demianzenkov/UWB-Open-RTLS-MCU/hardware/anchor/Photos/anchor_asm.png

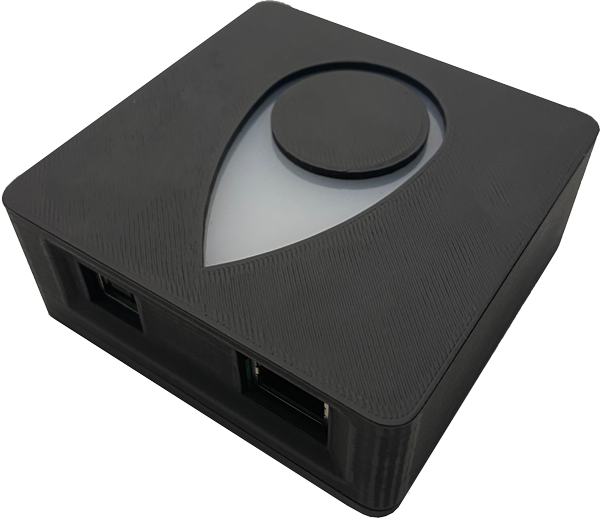
hardware/anchor/Photos/anchor_asm.png
