demianzenkov/UWB-Open-RTLS-MCU/hardware/anchor/Photos/anchor_case.png

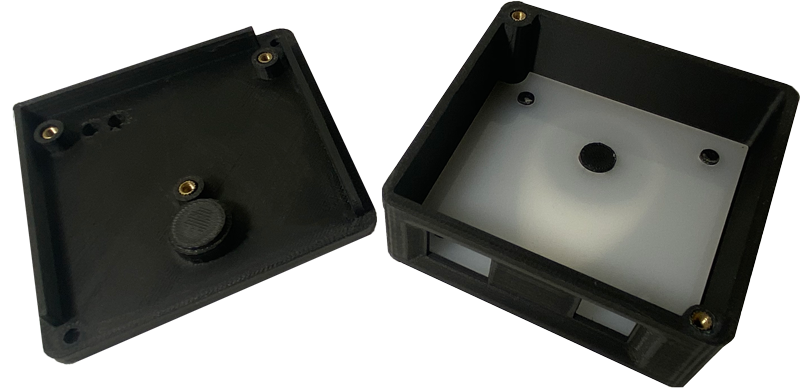
hardware/anchor/Photos/anchor_case.png
