demianzenkov/UWB-Open-RTLS-MCU/hardware/anchor/Photos/anchor_pcb.png

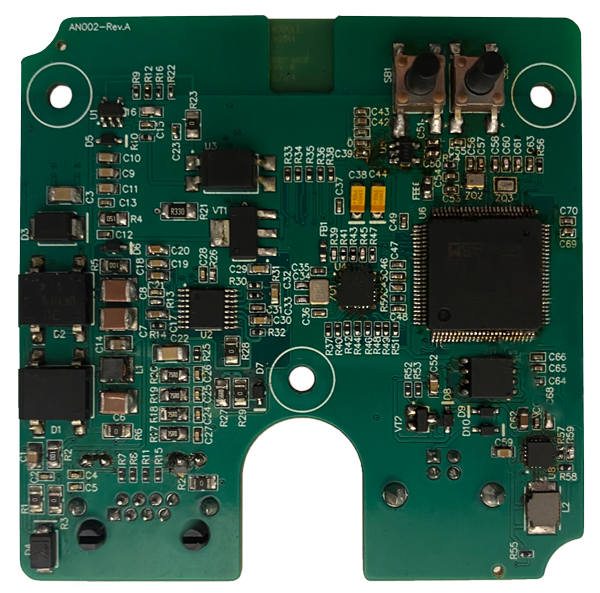
hardware/anchor/Photos/anchor_pcb.png
