demianzenkov/UWB-Open-RTLS-MCU/hardware/anchor/Photos/IMG_0143.JPG

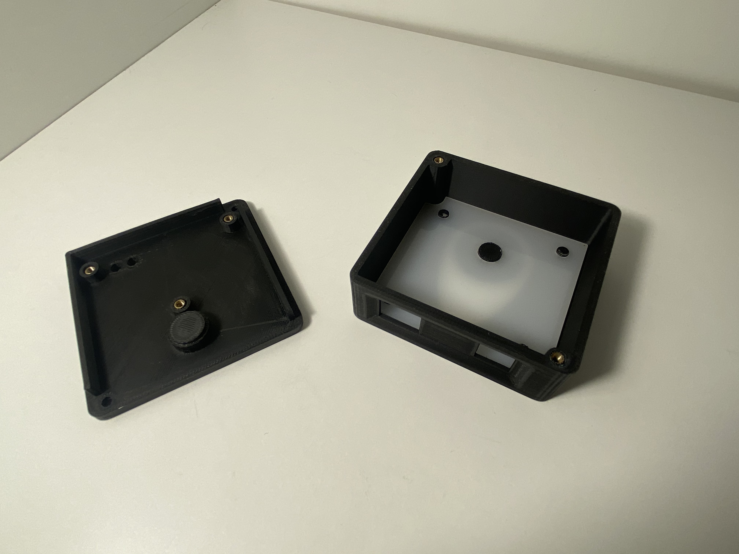
hardware/anchor/Photos/IMG_0143.JPG
