demianzenkov/UWB-Open-RTLS-MCU/hardware/anchor/Photos/IMG_0152.JPG

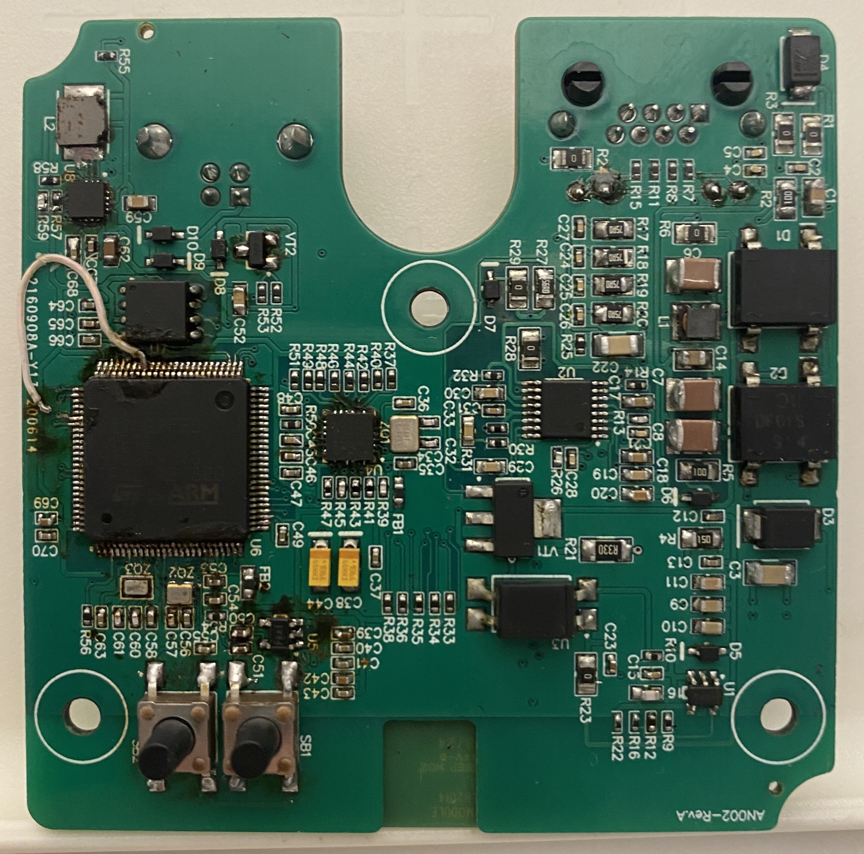
hardware/anchor/Photos/IMG_0152.JPG
