demianzenkov/UWB-Open-RTLS-MCU/hardware/anchor/Photos/IMG_0156.JPG

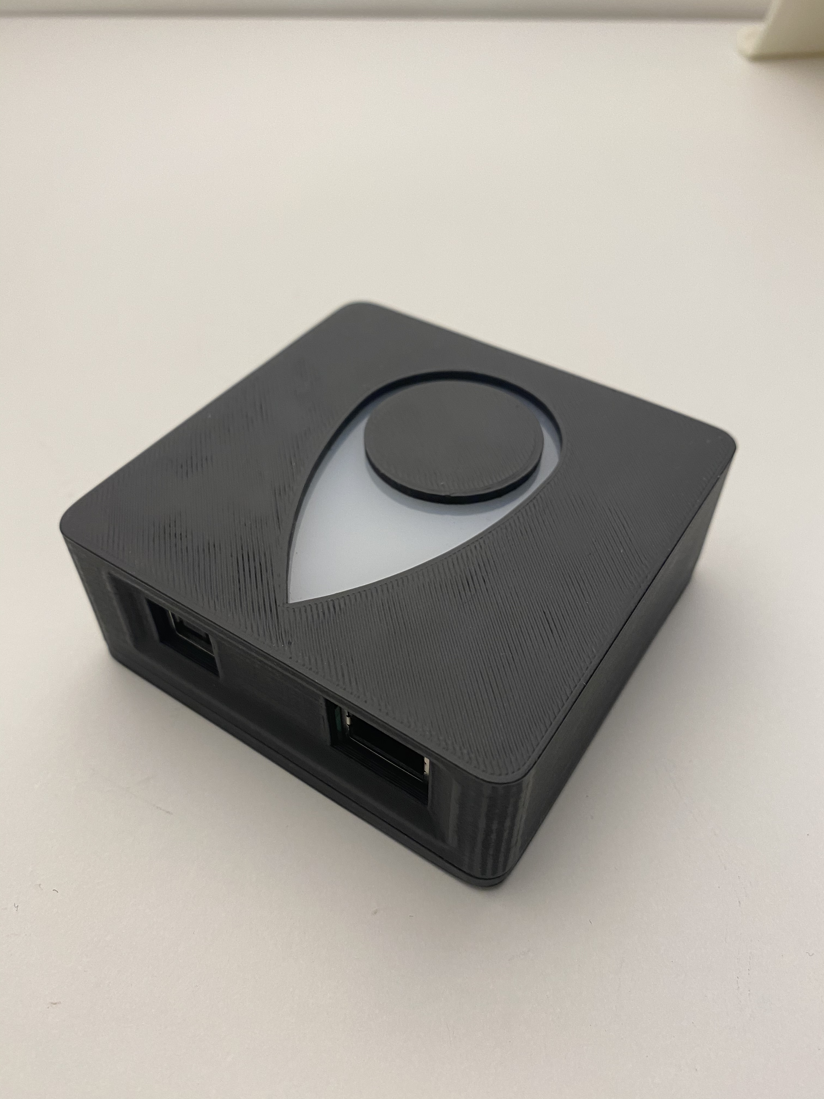
hardware/anchor/Photos/IMG_0156.JPG
