demianzenkov/UWB-Open-RTLS-MCU/hardware/anchor/Photos/IMG_0158.JPG

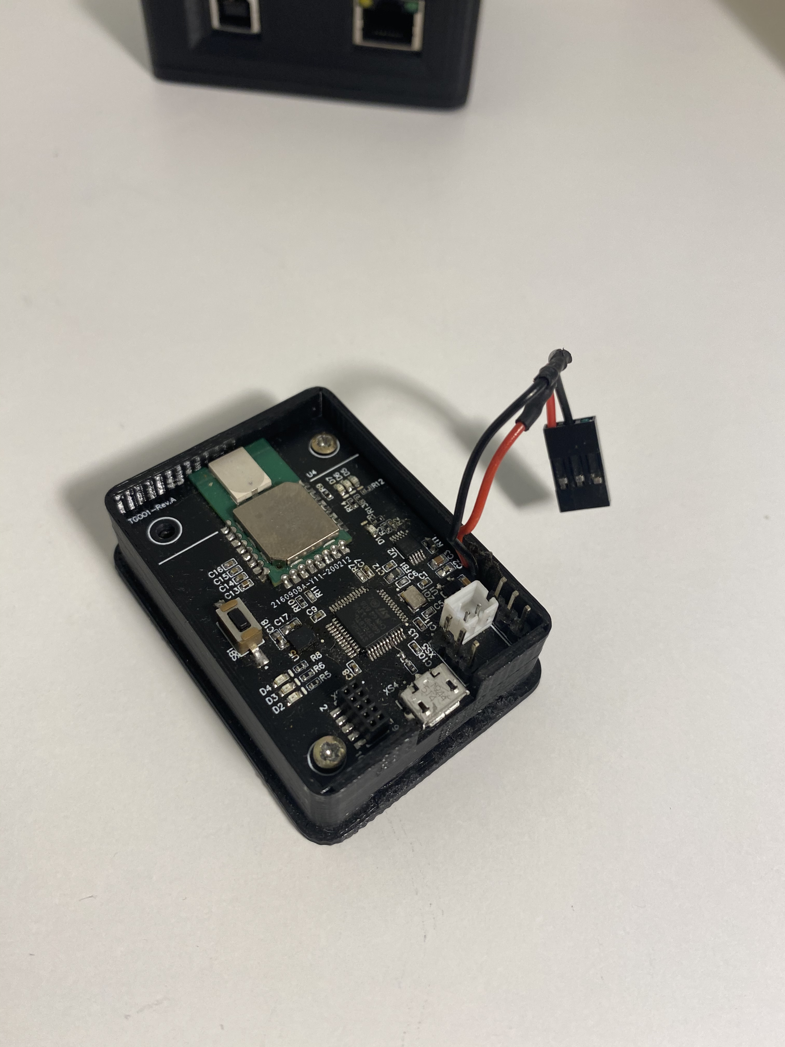
hardware/anchor/Photos/IMG_0158.JPG
