demianzenkov/UWB-Open-RTLS-MCU/hardware/anchor/Photos/IMG_0159.JPG

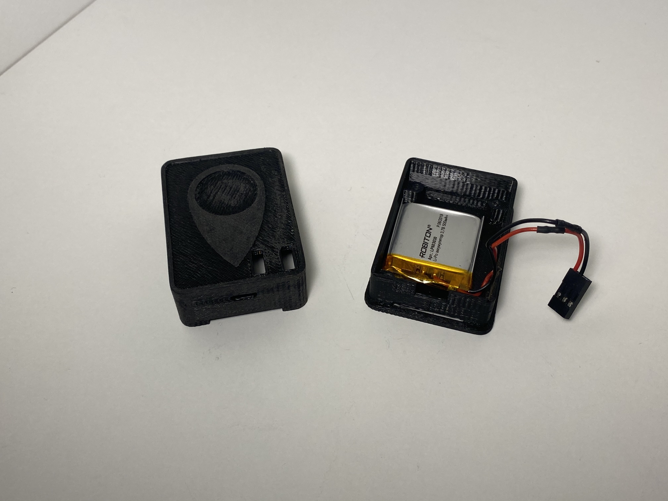
hardware/anchor/Photos/IMG_0159.JPG
