demianzenkov/UWB-Open-RTLS-MCU/hardware/anchor/Photos/IMG_0161.JPG

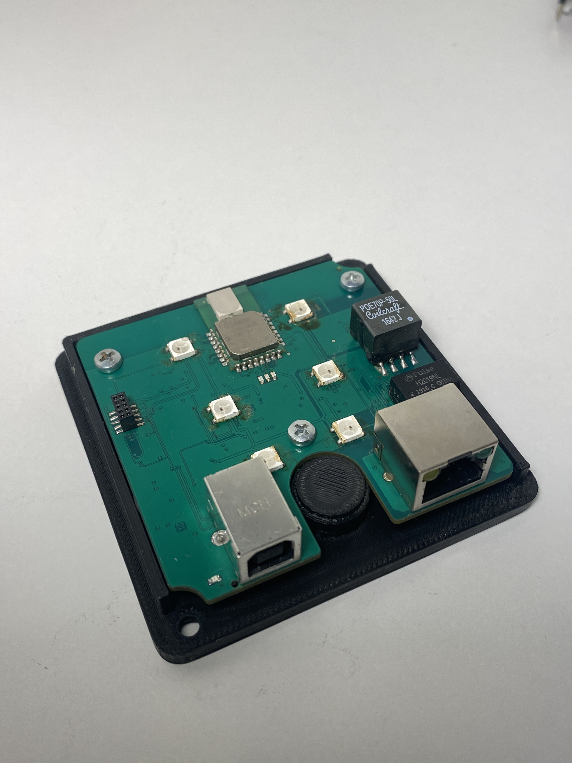
hardware/anchor/Photos/IMG_0161.JPG
