demianzenkov/UWB-Open-RTLS-MCU/hardware/anchor/Photos/tag_case.png

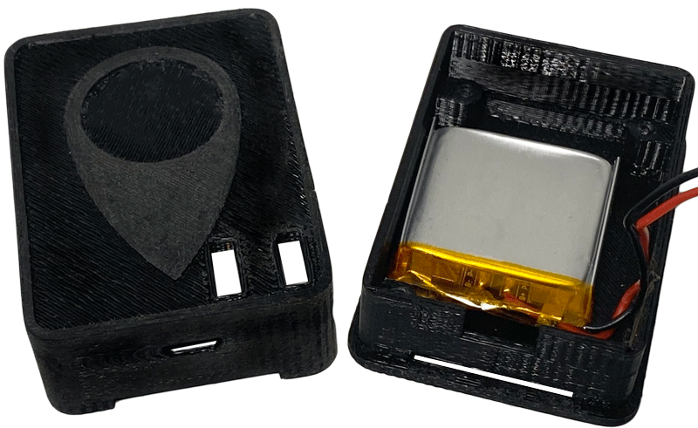
hardware/anchor/Photos/tag_case.png
