demianzenkov/UWB-Open-RTLS-MCU/hardware/anchor/Render/an_tag.png

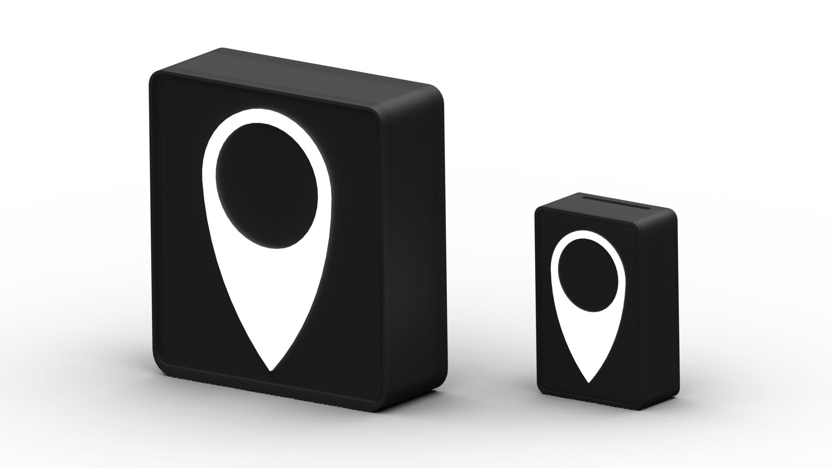
hardware/anchor/Render/an_tag.png
