demianzenkov/UWB-Open-RTLS-MCU/hardware/anchor/Render/AN_TAG_04.png

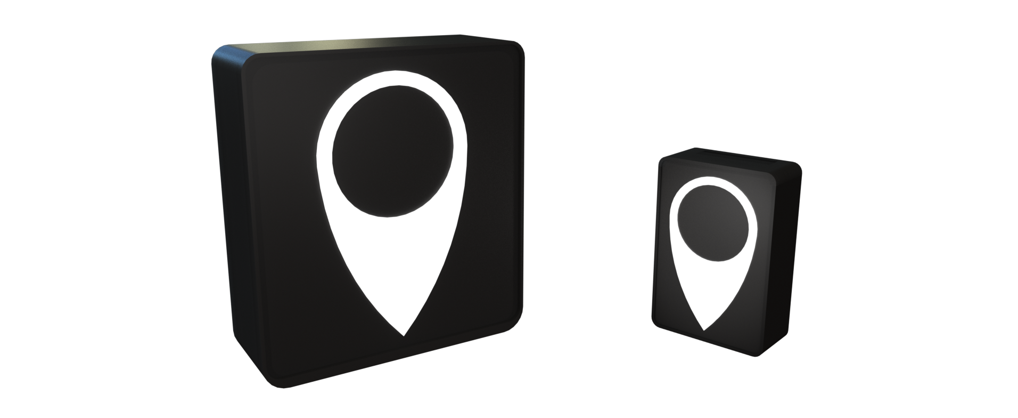
hardware/anchor/Render/AN_TAG_04.png
