demianzenkov/UWB-Open-RTLS-MCU/docs/anchor_assembly.gif

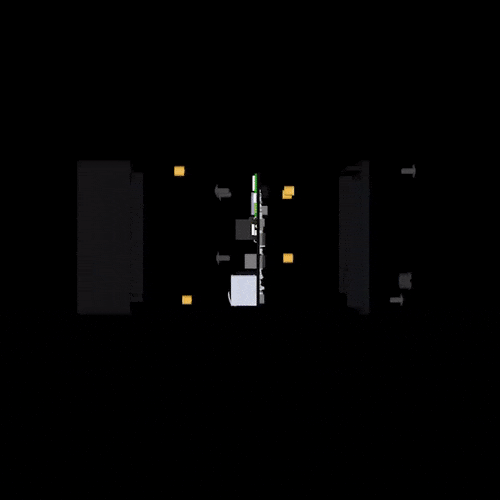
docs/anchor_assembly.gif
