demianzenkov/UWB-Open-RTLS-MCU/firmware/tag/User/Modules/une_twr.h

#define __UNE_TWR
#include "prj_defs.h"
#include "dwm1000.h"
#define UUS_TO_DWT_TIME 65536
#define POLL_TX_TO_RESP_RX_DLY_UUS 500
#define RESP_RX_TO_FINAL_TX_DLY_UUS 3100 //3000
#define RESP_RX_TIMEOUT_UUS 2700 	//2700 // Receive response timeout. NOTE 5
#define POLL_RX_TO_RESP_TX_DLY_UUS 3500				//2750
#define RESP_TX_TO_FINAL_RX_DLY_UUS 1000		//500
#define FINAL_RX_TIMEOUT_UUS 3700
#define PRE_TIMEOUT 8 			// Preamble tomeout. NOTE 6
#define POLL_MSG_SIZE	10
#define RESP_MSG_SIZE	12
#define FINAL_MSG_SIZE	29
#define DW_MSG_PREAMBLE_LEN	4
#define DEFAULT_TAG_ID		0x01
#define DEFAULT_ANCHOR_ID	0x01
#define START_POLL_N_H	0
#define START_POLL_N_L	0
#define START_RESP_N_H	0
#define START_RESP_N_L	0
#define START_FINAL_N_H	0
#define START_FINAL_N_L	0
#define MSG_TS_LEN 		5
#define FINAL_MSG_POLL_TX_TS_IDX	12
#define FINAL_MSG_RESP_RX_TS_IDX	17
#define FINAL_MSG_FINAL_TX_TS_IDX	22
#define MSG_TAG_IDX		4
#define MSG_AN_IDX		5
#define MSG_POLL_H_IDX		6
#define MSG_POLL_L_IDX		7
#define MSG_RESP_H_IDX		8
#define MSG_RESP_L_IDX		9
#define MSG_FINAL_H_IDX		10
#define MSG_FINAL_L_IDX		11
#define SPEED_OF_LIGHT 299702547	// metres per second
class UNE_TWR {
public:
  UNE_TWR(DWM1000 * dwm);
  ~UNE_TWR();
  static void initDWM();
  S08 twrInitiatorLoop(U08 an_id);
  S08 twrResponderLoop();
  static void final_msg_set_ts(uint8 *ts_field, uint64 ts);
  static void final_msg_get_ts(const uint8 *ts_field, uint64 *ts);
private:
  DWM1000 * dwm;
  U16 poll_frame_seq_nb;	// Tag
  U16 resp_frame_seq_nb;	// Anchor
  U16 final_frame_seq_nb;	// Tag
  U64 poll_rx_ts; 	// anchor(responder)
  U64 resp_tx_ts;	// anchor(responder)
  U64 final_rx_ts;	// anchor(responder)
  U64 poll_tx_ts;	// tag(initiator)
  U64 resp_rx_ts;	// tag(initiator)
  U64 final_tx_time;	// tag(initiator)
  U64 final_tx_ts;	// tag(initiator)
  U08 tag_id;		// anchor(initiator)
  double tof;		// anchor(initiator)
  float distance;	// anchor(initiator)
  U08 poll_msg[POLL_MSG_SIZE] = {'T', 'W', 'R', 'P',
			DEFAULT_TAG_ID,
			DEFAULT_ANCHOR_ID,
			START_POLL_N_H,
			START_POLL_N_L,
  			0, 0};		// CRC
  U08 resp_msg[RESP_MSG_SIZE] = {'T', 'W', 'R', 'R',
  			DEFAULT_TAG_ID,
			DEFAULT_ANCHOR_ID,
			START_POLL_N_H,
			START_POLL_N_L,
			START_RESP_N_H,
			START_RESP_N_L,
  			0, 0};		// CRC
  U08 final_msg[FINAL_MSG_SIZE] = {'T', 'W', 'R', 'F',
			DEFAULT_TAG_ID,
			DEFAULT_ANCHOR_ID,
			START_POLL_N_H,
			START_POLL_N_L,
			START_RESP_N_H,
			START_RESP_N_L,
			START_FINAL_N_H,
			START_FINAL_N_L,
			0,0,0,0,0,	// POLL TX
			0,0,0,0,0,	// RESP RX
			0,0,0,0,0,	// FINAL TX
  			0, 0};		// CRC
};
