demianzenkov/UWB-Open-RTLS-MCU/firmware/anchor/Inc/main.h

#define DW_WUP_Pin GPIO_PIN_2
#define DW_WUP_GPIO_Port GPIOE
#define DW_RESET_Pin GPIO_PIN_3
#define DW_RESET_GPIO_Port GPIOE
#define DW_RESET_EXTI_IRQn EXTI3_IRQn
#define DW_IRQn_Pin GPIO_PIN_4
#define DW_IRQn_GPIO_Port GPIOE
#define DW_IRQn_EXTI_IRQn EXTI4_IRQn
#define DW_NSS_Pin GPIO_PIN_4
#define DW_NSS_GPIO_Port GPIOA
#define DW_SCK_Pin GPIO_PIN_5
#define DW_SCK_GPIO_Port GPIOA
#define DW_MISO_Pin GPIO_PIN_6
#define DW_MISO_GPIO_Port GPIOA
#define FLASH_SCK_Pin GPIO_PIN_10
#define FLASH_SCK_GPIO_Port GPIOB
#define FLASH_MISO_Pin GPIO_PIN_14
#define FLASH_MISO_GPIO_Port GPIOB
#define FLASH_MOSI_Pin GPIO_PIN_15
#define FLASH_MOSI_GPIO_Port GPIOB
#define FLASH_CS_Pin GPIO_PIN_8
#define FLASH_CS_GPIO_Port GPIOD
#define LED_DIN_Pin GPIO_PIN_8
#define LED_DIN_GPIO_Port GPIOA
#define LED_VDD_Pin GPIO_PIN_1
#define LED_VDD_GPIO_Port GPIOD
#define DW_MOSI_Pin GPIO_PIN_5
#define DW_MOSI_GPIO_Port GPIOB
