demianzenkov/UWB-Open-RTLS-MCU/firmware/tag/Src/main.cpp

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

/* Includes ------------------------------------------------------------------*/
#include "main.h"
#include "cmsis_os.h"
#include "usb_device.h"

/* USER CODE BEGIN Includes */
#include "tsk_dwm.h"
#include "tsk_lsm.h"
#include "tsk_usb.h"
#include "tsk_event.h"
#include "settings.h"

/* USER CODE END Includes */

SPI_HandleTypeDef hspi1;
SPI_HandleTypeDef hspi2;

TIM_HandleTypeDef htim6;

UART_HandleTypeDef huart1;

osThreadId initTaskHandle;
/* USER CODE BEGIN PV */
extern TskDWM tskDWM;
extern TskLSM tskLSM;
extern TskUSB tskUSB;
extern TskEvent tskEvent;

extern DeviceSettings settings;
volatile uint32_t us_tick = 0;
/* USER CODE END PV */


static void MX_GPIO_Init(void);
static void MX_SPI1_Init(void);
static void MX_SPI2_Init(void);
static void MX_TIM6_Init(void);
static void MX_USART1_UART_Init(void);
void StartDefaultTask(void const * argument);

/**
  * @brief  The application entry point.
  * @retval int
  */
int main(void)
{
  

  /* MCU Configuration-------------------------------------------------------- */

  /* Reset of all peripherals, Initializes the Flash interface and the Systick. */
  HAL_Init();

  /* Configure the system clock */
  SystemClock_Config();

  /* Initialize all configured peripherals */
  MX_GPIO_Init();
  MX_SPI1_Init();
  MX_SPI2_Init();
  MX_USART1_UART_Init();
//  MX_TIM6_Init();
  /* USER CODE BEGIN 2 */
  settings.init();
  /* USER CODE END 2 */

  /* USER CODE BEGIN RTOS_MUTEX */
  /* add mutexes, ... */
  /* USER CODE END RTOS_MUTEX */

  /* USER CODE BEGIN RTOS_SEMAPHORES */
  /* add semaphores, ... */
  /* USER CODE END RTOS_SEMAPHORES */

  /* USER CODE BEGIN RTOS_TIMERS */
  /* start timers, add new ones, ... */
  /* USER CODE END RTOS_TIMERS */

  /* USER CODE BEGIN RTOS_QUEUES */
  /* add queues, ... */
  /* USER CODE END RTOS_QUEUES */

  /* Create the thread(s) */
  /* definition and creation of initTask */
  osThreadDef(initTask, StartDefaultTask, osPriorityNormal, 0, 128);
  initTaskHandle = osThreadCreate(osThread(initTask), NULL);

  /* USER CODE BEGIN RTOS_THREADS */
  /* add threads, ... */
  tskDWM.createTask();
  tskUSB.createTask();
  tskEvent.createTask();
//  tskLSM.createTask();
  /* USER CODE END RTOS_THREADS */

  /* Start scheduler */
  osKernelStart();
  
  /* We should never get here as control is now taken by the scheduler */

  /* Infinite loop */
  /* USER CODE BEGIN WHILE */
  while (1)
  { 
    /* USER CODE END WHILE */

    /* USER CODE BEGIN 3 */
  }
  /* USER CODE END 3 */
}

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
/* USER CODE BEGIN Header_StartDefaultTask */
/**
  * @brief  Function implementing the initTask thread.
  * @param  argument: Not used 
  * @retval None
  */
/* USER CODE END Header_StartDefaultTask */
void StartDefaultTask(void const * argument)
{                
  /* init code for USB_DEVICE */
  MX_USB_DEVICE_Init();

  /* USER CODE BEGIN 5 */
  /* Infinite loop */
  for(;;)
  {
    HAL_GPIO_TogglePin(LED1_GPIO_Port, LED1_Pin);
    osDelay(1000);
    HAL_GPIO_TogglePin(LED1_GPIO_Port, LED1_Pin);
    osDelay(1000);
  }
  /* USER CODE END 5 */ 
}

/**
  * @brief  Period elapsed callback in non blocking mode
  * @note   This function is called  when TIM3 interrupt took place, inside
  * HAL_TIM_IRQHandler(). It makes a direct call to HAL_IncTick() to increment
  * a global variable "uwTick" used as application time base.
  * @param  htim : TIM handle
  * @retval None
  */
void HAL_TIM_PeriodElapsedCallback(TIM_HandleTypeDef *htim)
{
  if (htim->Instance == TIM3) {
    HAL_IncTick();
  }
  /* USER CODE BEGIN Callback 1 */
  if (htim->Instance == TIM6){
    us_tick++;  
  }
  /* USER CODE END Callback 1 */
}

/**
  * @brief  This function is executed in case of error occurrence.
  * @retval None
  */
void Error_Handler(void)
{
  /* USER CODE BEGIN Error_Handler_Debug */
  /* User can add his own implementation to report the HAL error return state */

  /* USER CODE END Error_Handler_Debug */
}

#ifdef  USE_FULL_ASSERT
/**
  * @brief  Reports the name of the source file and the source line number
  *         where the assert_param error has occurred.
  * @param  file: pointer to the source file name
  * @param  line: assert_param error line source number
  * @retval None
  */
void assert_failed(uint8_t *file, uint32_t line)
{ 
  /* USER CODE BEGIN 6 */
  /* User can add his own implementation to report the file name and line number,
     tex: printf("Wrong parameters value: file %s on line %d\r\n", file, line) */
  /* USER CODE END 6 */
}
#endif /* USE_FULL_ASSERT */

/************************ (C) COPYRIGHT STMicroelectronics *****END OF FILE****/
