demianzenkov/UWB-Open-RTLS-MCU/firmware/anchor/User/modules/settings.h

#ifndef __DEV_SETTINGS
#define __DEV_SETTINGS

#include "settings_pb.h"
#include "net_conf.h"

#define DEFAULT_DEVICE_ID_U32		0xAABBDDCC
#define DEFAULT_TX_ANT_DLY 		16436
#define DEFAULT_RX_ANT_DLY 		16436
#define DEFAULT_TWR_ANCHOR_CNT		4
#define DEFAULT_POLL_PERIOD		1000

class DeviceSettings
{
public:
  DeviceSettings();
  S08 init();
  
  S08 setDefaultSettings();
  S08 getSettings(U08 ** buf, U16 * len);
  S08 setSettingsPb(U08 * buf, U16 len);
  
private:
  S08 readSettingsFromFlash();
  S08 writeSettingsToFlash(U08 * buf, U16 len);
  
public:
  SettingsPB pb_settings;
  NetConfig net_conf;
  
  static U08 MAC_ADDR[6];
  
};

extern DeviceSettings settings;

#endif /* __DEV_SETTINGS */
