demianzenkov/UWB-Open-RTLS-MCU/firmware/anchor/Src/lwip.cpp

/**
 ******************************************************************************
  * File Name          : LWIP.c
  * Description        : This file provides initialization code for LWIP
  *                      middleWare.
  ******************************************************************************
  * @attention
  *
  * <h2><center>&copy; Copyright (c) 2020 STMicroelectronics.
  * All rights reserved.</center></h2>
  *
  * This software component is licensed by ST under Ultimate Liberty license
  * SLA0044, the "License"; You may not use this file except in compliance with
  * the License. You may obtain a copy of the License at:
  *                             www.st.com/SLA0044
  *
  ******************************************************************************
  */
  
/* Includes ------------------------------------------------------------------*/
#include "lwip.h"
#include "lwip/init.h"
#include "lwip/netif.h"
#if defined ( __CC_ARM )  /* MDK ARM Compiler */
#include "lwip/sio.h"
#endif /* MDK ARM Compiler */

/* USER CODE BEGIN 0 */
#include "ethernetif.h"
#include "settings.h"

/* USER CODE END 0 */
/* ETH Variables initialization ----------------------------------------------*/
void Error_Handler(void);

/* Variables Initialization */
struct netif gnetif;
ip4_addr_t ipaddr;
ip4_addr_t netmask;
ip4_addr_t gw;
uint8_t IP_ADDRESS[4];
uint8_t NETMASK_ADDRESS[4];
uint8_t GATEWAY_ADDRESS[4];

/**
  * LwIP initialization function
  */
void MX_LWIP_Init(void)
{
  /* USER CODE BEGIN LWIP_INIT */
  /* IP addresses initialization */
  
  IP_ADDRESS[0] = settings.net_conf.getDeviceIp()[0];
  IP_ADDRESS[1] = settings.net_conf.getDeviceIp()[1];
  IP_ADDRESS[2] = settings.net_conf.getDeviceIp()[2];
  IP_ADDRESS[3] = settings.net_conf.getDeviceIp()[3];
  NETMASK_ADDRESS[0] = settings.net_conf.getSubnetMask()[0];
  NETMASK_ADDRESS[1] = settings.net_conf.getSubnetMask()[1];
  NETMASK_ADDRESS[2] = settings.net_conf.getSubnetMask()[2];
  NETMASK_ADDRESS[3] = settings.net_conf.getSubnetMask()[3];
  GATEWAY_ADDRESS[0] = settings.net_conf.getGatewayIp()[0];
  GATEWAY_ADDRESS[1] = settings.net_conf.getGatewayIp()[1];
  GATEWAY_ADDRESS[2] = settings.net_conf.getGatewayIp()[2];
  GATEWAY_ADDRESS[3] = settings.net_conf.getGatewayIp()[3];
  /* USER CODE END LWIP_INIT */
  
  /* Initilialize the LwIP stack with RTOS */
  tcpip_init( NULL, NULL );

  /* IP addresses initialization without DHCP (IPv4) */
  IP4_ADDR(&ipaddr, IP_ADDRESS[0], IP_ADDRESS[1], IP_ADDRESS[2], IP_ADDRESS[3]);
  IP4_ADDR(&netmask, NETMASK_ADDRESS[0], NETMASK_ADDRESS[1] , NETMASK_ADDRESS[2], NETMASK_ADDRESS[3]);
  IP4_ADDR(&gw, GATEWAY_ADDRESS[0], GATEWAY_ADDRESS[1], GATEWAY_ADDRESS[2], GATEWAY_ADDRESS[3]);

  /* add the network interface (IPv4/IPv6) with RTOS */
  netif_add(&gnetif, &ipaddr, &netmask, &gw, NULL, &ethernetif_init, &tcpip_input);

  /* Registers the default network interface */
  netif_set_default(&gnetif);

  if (netif_is_link_up(&gnetif))
  {
    /* When the netif is fully configured this function must be called */
    netif_set_up(&gnetif);
  }
  else
  {
    /* When the netif link is down this function must be called */
    netif_set_down(&gnetif);
  }

}

#ifdef USE_OBSOLETE_USER_CODE_SECTION_4
/* Kept to help code migration. (See new 4_1, 4_2... sections) */
/* Avoid to use this user section which will become obsolete. */
#endif

#if defined ( __CC_ARM )  /* MDK ARM Compiler */
/**
 * Opens a serial device for communication.
 *
 * @param devnum device number
 * @return handle to serial device if successful, NULL otherwise
 */
sio_fd_t sio_open(u8_t devnum)
{
  sio_fd_t sd;

/* USER CODE BEGIN 7 */
  sd = 0; // dummy code
/* USER CODE END 7 */
	
  return sd;
}

/**
 * Sends a single character to the serial device.
 *
 * @param c character to send
 * @param fd serial device handle
 *
 * @note This function will block until the character can be sent.
 */
void sio_send(u8_t c, sio_fd_t fd)
{
}

/**
 * Reads from the serial device.
 *
 * @param fd serial device handle
 * @param data pointer to data buffer for receiving
 * @param len maximum length (in bytes) of data to receive
 * @return number of bytes actually received - may be 0 if aborted by sio_read_abort
 *
 * @note This function will block until data can be received. The blocking
 * can be cancelled by calling sio_read_abort().
 */
u32_t sio_read(sio_fd_t fd, u8_t *data, u32_t len)
{
  u32_t recved_bytes;

/* USER CODE BEGIN 9 */
  recved_bytes = 0; // dummy code
/* USER CODE END 9 */	
  return recved_bytes;
}

/**
 * Tries to read from the serial device. Same as sio_read but returns
 * immediately if no data is available and never blocks.
 *
 * @param fd serial device handle
 * @param data pointer to data buffer for receiving
 * @param len maximum length (in bytes) of data to receive
 * @return number of bytes actually received
 */
u32_t sio_tryread(sio_fd_t fd, u8_t *data, u32_t len)
{
  u32_t recved_bytes;

/* USER CODE BEGIN 10 */
  recved_bytes = 0; // dummy code
/* USER CODE END 10 */	
  return recved_bytes;
}
#endif /* MDK ARM Compiler */

/************************ (C) COPYRIGHT STMicroelectronics *****END OF FILE****/
