demianzenkov/UWB-Open-RTLS-MCU/firmware/anchor/User/tasks/tsk_dwm.h

#ifndef __TSK_DWM
#define __TSK_DWM

#include "main.h"
#include "cmsis_os.h"
#include "dwm1000.h"
#include "une_twr.h"
#include "une_tdoa.h"

class TskDWM 
{
public:
  TskDWM();
  ~TskDWM();
  void createTask();
  static void task(void const *arg);
  
public:
  SemaphoreHandle_t xSemUSBReady;
  
public:
  DWM1000 dwm;
  UNE_TDOA une_tdoa;
  UNE_TWR une_twr;  
};

extern TskDWM tskDWM;

#endif
