demianzenkov/UWB-Open-RTLS-MCU/firmware/anchor/User/decawave/platform/deca_sleep.c

/*! ----------------------------------------------------------------------------
 * @file    deca_sleep.c
 * @brief   platform dependent sleep implementation
 *
 * @attention
 *
 * Copyright 2015 (c) DecaWave Ltd, Dublin, Ireland.
 *
 * All rights reserved.
 *
 * @author DecaWave
 */

#include "deca_device_api.h"
#include "sleep.h"
#include "deca_port.h"

/* Wrapper function to be used by decadriver. Declared in deca_device_api.h */
__INLINE void deca_sleep(unsigned int time_ms)
{
	Sleep(time_ms);
}
